Yu-taguchi/1CH-EGT-to-CAN-BUS-MODULE/Board files/Rev. 1.0/PHOTO1.jpg

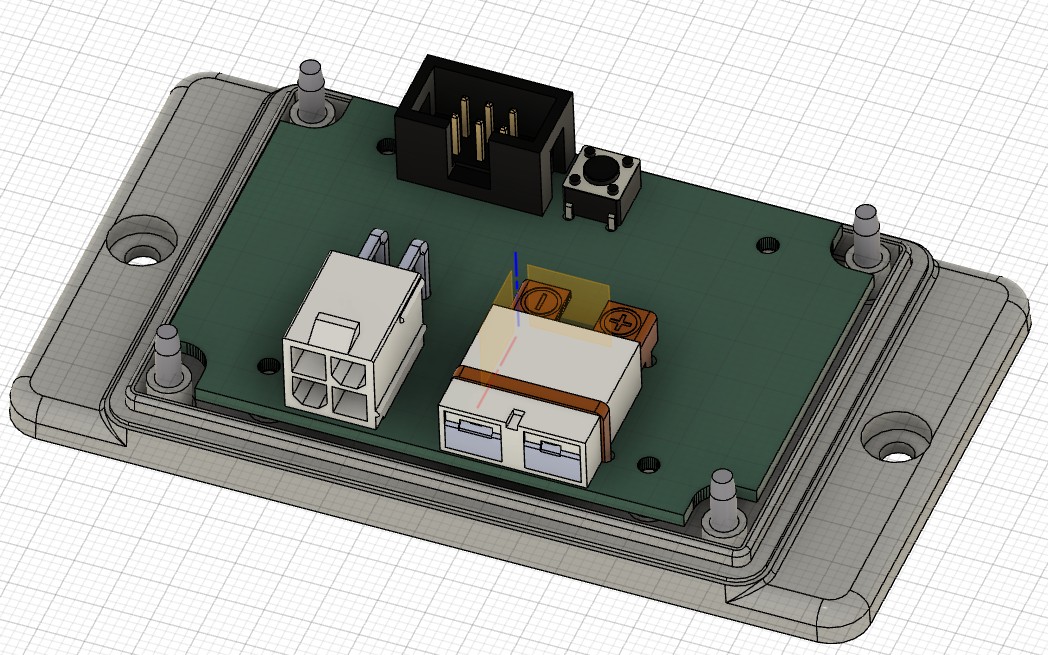
Board files/Rev. 1.0/PHOTO1.jpg
